elabree/ZeDMD-5.1.8-WIFI-128x32/data/The_Arcade.png

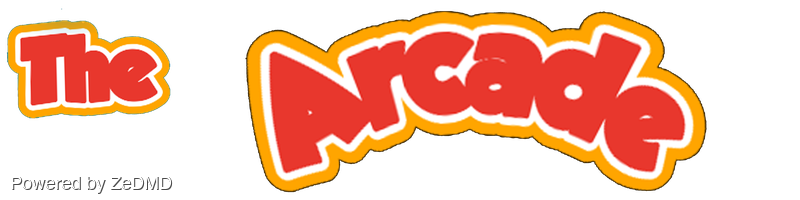
data/The_Arcade.png
