elabree/ZeDMD-5.1.8-WIFI-128x32/docs/images/IMG_5077.jpeg

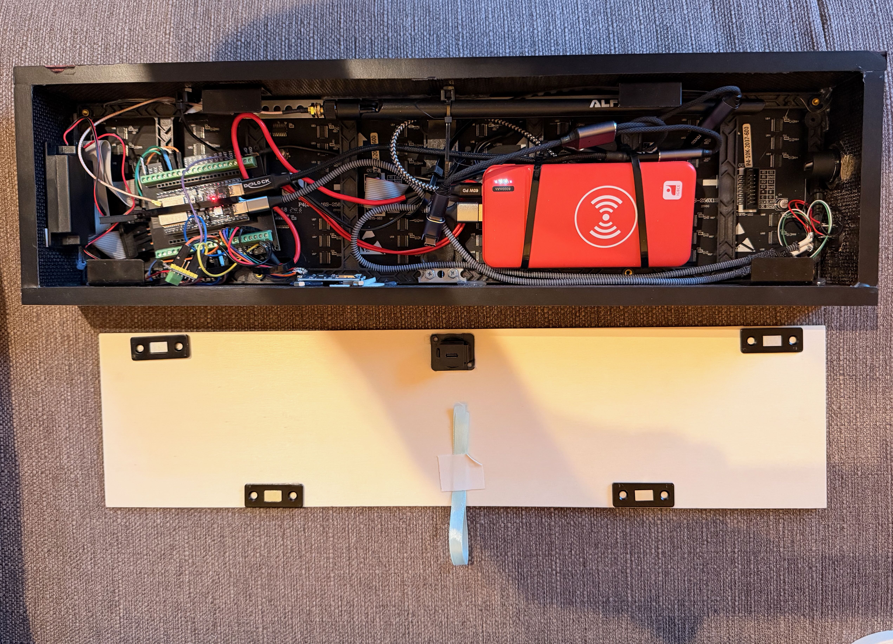
docs/images/IMG_5077.jpeg
