elabree/ZeDMD-5.1.8-WIFI-128x32/KiCad/ZeDMD_WiFi/docs/ZeDMD_WiFi_bottom.png

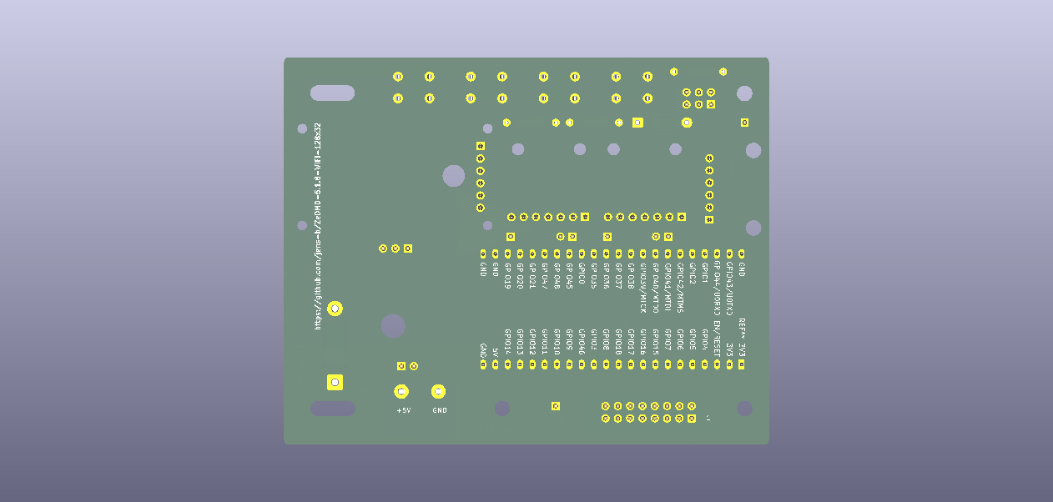
KiCad/ZeDMD_WiFi/docs/ZeDMD_WiFi_bottom.png
