elabree/ZeDMD-5.1.8-WIFI-128x32/src/displayDriver.h

#ifndef DISPLAYDRIVER_H
#define DISPLAYDRIVER_H

#include <stdint.h>

class DisplayDriver {
 public:
  /// @brief Check if display has scaling modes
  /// @return true if scaling modes are available
  virtual bool HasScalingModes() = 0;

  /// @brief Get the names of the scaling modes
  /// @return a static array of scaling mode names
  virtual const char **GetScalingModes() = 0;

  /// @brief Get the number of available scaling modes
  /// @return the count of available scaling modes
  virtual uint8_t GetScalingModeCount() = 0;

  /// @brief Get the current scaling mode
  /// @return the count of available scaling modes
  virtual uint8_t GetCurrentScalingMode() = 0;

  /// @brief Set the scaling mode
  virtual void SetCurrentScalingMode(uint8_t mode) = 0;

  /// @brief Draw a RGB888 pixel
  /// @param x X coordinate
  /// @param y Y coordinate
  /// @param r 8 bit red color
  /// @param g 8 bit green color
  /// @param b 8 bit blue color
  virtual void DrawPixel(uint16_t x, uint16_t y, uint8_t r, uint8_t g,
                         uint8_t b) = 0;

  /// @brief Draw a RGB565 pixel
  /// @param x X coordinate
  /// @param y Y coordinate
  /// @param color 16 bit RGB565 color
  virtual void DrawPixel(uint16_t x, uint16_t y, uint16_t color) = 0;

  /// @brief Clear screen
  virtual void ClearScreen() = 0;

  /// @brief Set brightness of display
  /// @param level 0-15 levels
  virtual void SetBrightness(uint8_t level) = 0;

  /// @brief Fill entire screen with one color
  /// @param r 8 bit red color
  /// @param g 8 bit green color
  /// @param b 8 bit blue color
  virtual void FillScreen(uint8_t r, uint8_t g, uint8_t b) = 0;

  /// @brief Write text to display
  /// @param text string of text
  /// @param x X coordinate
  /// @param y Y coordinate
  /// @param r 8 bit red color
  /// @param g 8 bit green color
  /// @param b 8 bit blue color
  /// @param transparent background transparent
  /// @param inverted colors inverted
  virtual void DisplayText(const char *text, uint16_t x, uint16_t y, uint8_t r,
                           uint8_t g, uint8_t b, bool transparent = false,
                           bool inverted = false) = 0;

  virtual void DisplayTextScaled(const char *text, uint16_t x, uint16_t y,
                                  uint8_t r, uint8_t g, uint8_t b,
                                  uint8_t scale = 1) {
    DisplayText(text, x, y, r, g, b);
  }

#ifdef FONT_TEST_ENABLED
  virtual void RenderFontTestToBuffer(uint8_t * /*buf*/, const char * /*text*/,
                                       const char * /*fontName*/, uint8_t /*lines*/,
                                       uint8_t /*r*/, uint8_t /*g*/, uint8_t /*b*/) {}
  virtual const char* GetFontListJSON() { return "[]"; }
#endif

  virtual void DisplayTextGFX(const char *text, int16_t x, uint8_t r,
                               uint8_t g, uint8_t b) {
    DisplayText(text, (uint16_t)(x < 0 ? 0 : x), 0, r, g, b);
  }

  virtual uint16_t GetTextGFXWidth(const char *text) {
    return (uint16_t)(strlen(text) * 12);
  }

  virtual void EraseVLine(int16_t x) {}
  virtual void RenderTextGFXToBuffer(uint8_t *buf, const char *text, int16_t x,
                                     uint8_t r, uint8_t g, uint8_t b) {}
  virtual void RenderRadioToBuffer(uint8_t *buf, const char *station,
                                   const char *title,
                                   int16_t stationX, int16_t titleX,
                                   uint8_t stR, uint8_t stG, uint8_t stB,
                                   uint8_t r, uint8_t g, uint8_t b) {}
  virtual uint16_t GetRadioTitleWidth(const char *text) {
    return (uint16_t)(strlen(text) * 9);
  }

  /// @brief RGB888 24bit Zone fill
  /// @param idx index
  /// @param pBuffer buffer with pixel data [R,G,B]
  /// @return
  virtual void FillZoneRaw(uint8_t idx, uint8_t *pBuffer) = 0;

  /// @brief RGB565 16 bit Zone Fill
  /// @param idx index
  /// @param pBuffer buffer with pixel data 16 bits
  /// @return
  virtual void FillZoneRaw565(uint8_t idx, uint8_t *pBuffer) = 0;

  virtual void ClearZone(uint8_t idx) = 0;

  /// @brief Fill fullscreen with current renderBuffer
  /// @return
  virtual void FillPanelRaw(uint8_t *pBuffer) = 0;

  virtual ~DisplayDriver() {}  // Virtual destructor
};

#endif  // DISPLAYDRIVER_H
