elabree/ZeDMD-5.1.8-WIFI-128x32/src/displays/LEDMatrix.cpp

#ifdef DISPLAY_LED_MATRIX
#include "LEDMatrix.h"

#include "fonts/tiny4x6.h"
#include <Fonts/FreeSansBold12pt7b.h>
#include <Fonts/FreeSans9pt7b.h>

#ifdef FONT_TEST_ENABLED
#include "fonts/hzeller_tom_thumb.h"
#include "fonts/hzeller_4x6.h"
#include "fonts/hzeller_5x7.h"
#include "fonts/hzeller_5x8.h"
#include "fonts/hzeller_6x9.h"
#include "fonts/hzeller_6x10.h"
#include "fonts/hzeller_6x12.h"
#include "fonts/hzeller_6x13.h"
#include "fonts/hzeller_6x13B.h"
#include "fonts/hzeller_6x13O.h"
#include "fonts/hzeller_7x13.h"
#include "fonts/hzeller_7x13B.h"
#include "fonts/hzeller_7x13O.h"
#include "fonts/hzeller_7x14.h"
#include "fonts/hzeller_7x14B.h"
#include "fonts/hzeller_8x13.h"
#include "fonts/hzeller_8x13B.h"
#include "fonts/hzeller_8x13O.h"
#include "fonts/hzeller_9x15.h"
#include "fonts/hzeller_9x15B.h"
#include "fonts/hzeller_9x18.h"
#include "fonts/hzeller_9x18B.h"
#include "fonts/hzeller_10x20.h"
#include "fonts/hzeller_clR6x12.h"
#include "fonts/hzeller_helvR12.h"
#include "fonts/hzeller_texgyre_27.h"

struct HzFontEntry { const char *name; const GFXfont *font; };
static const HzFontEntry kFonts[] = {
  {"tom-thumb",    &tom_thumb6pt7b},
  {"4x6",          &hz4x66pt7b},
  {"5x7",          &hz5x77pt7b},
  {"5x8",          &hz5x88pt7b},
  {"6x9",          &hz6x99pt7b},
  {"6x10",         &hz6x1010pt7b},
  {"6x12",         &hz6x1212pt7b},
  {"6x13",         &hz6x1313pt7b},
  {"6x13B",        &hz6x13B13pt7b},
  {"6x13O",        &hz6x13O13pt7b},
  {"7x13",         &hz7x1313pt7b},
  {"7x13B",        &hz7x13B13pt7b},
  {"7x13O",        &hz7x13O13pt7b},
  {"7x14",         &hz7x1414pt7b},
  {"7x14B",        &hz7x14B14pt7b},
  {"8x13",         &hz8x1313pt7b},
  {"8x13B",        &hz8x13B13pt7b},
  {"8x13O",        &hz8x13O13pt7b},
  {"9x15",         &hz9x1515pt7b},
  {"9x15B",        &hz9x15B15pt7b},
  {"9x18",         &hz9x1818pt7b},
  {"9x18B",        &hz9x18B18pt7b},
  {"10x20",        &hz10x2020pt7b},
  {"clR6x12",      &clR6x1212pt7b},
  {"helvR12",      &helvR1212pt7b},
  {"texgyre-27",   &texgyre_2727pt7b},
  {"FreeSans9",    &FreeSans9pt7b},
  {"FreeSansBold12", &FreeSansBold12pt7b},
};
static const uint8_t kFontCount = sizeof(kFonts) / sizeof(kFonts[0]);

static const GFXfont* findFont(const char *name) {
  for (uint8_t i = 0; i < kFontCount; i++)
    if (strcmp(kFonts[i].name, name) == 0) return kFonts[i].font;
  return &FreeSans9pt7b;
}

void LedMatrix::RenderFontTestToBuffer(uint8_t *buf, const char *text,
                                        const char *fontName, uint8_t lines,
                                        uint8_t r, uint8_t g, uint8_t b) {
  const GFXfont *f = findFont(fontName);
  memset(buf, 0, (size_t)TOTAL_WIDTH * TOTAL_HEIGHT * 3);
  textCanvas->fillScreen(0);
  textCanvas->setFont(f);
  textCanvas->setTextWrap(false);

  // Cursor y=0: y1 is then a relative offset (negative for ascenders)
  int16_t x1, y1; uint16_t tw, th;
  textCanvas->getTextBounds(text, 0, 0, &x1, &y1, &tw, &th);

  int16_t lineH  = f ? (int16_t)f->yAdvance : (int16_t)th + 1;
  // Total height of the text block (visual pixels)
  int16_t blockH = (int16_t)(lines - 1) * lineH + (int16_t)th;
  // Top edge of the block centered, then derive baseline of the first line
  int16_t topY      = ((int16_t)TOTAL_HEIGHT - blockH) / 2;
  int16_t baseline0 = topY - y1;  // y1 is negative → baseline0 > topY

  // Horizontal centering (same for all lines, same text)
  int16_t cx = ((int16_t)TOTAL_WIDTH - (int16_t)tw) / 2 - x1;
  if (cx < 0) cx = 0;

  uint16_t col = ((uint16_t)(r & 0xF8) << 8) | ((uint16_t)(g & 0xFC) << 3) | (b >> 3);
  textCanvas->setTextColor(col);

  for (uint8_t l = 0; l < lines; l++) {
    int16_t cy = baseline0 + l * lineH;
    if (cy >= (int16_t)TOTAL_HEIGHT) break;
    textCanvas->setCursor(cx, cy);
    textCanvas->print(text);
  }
  textCanvas->setFont(nullptr);

  const uint16_t *pixels = textCanvas->getBuffer();
  const uint32_t n = (uint32_t)TOTAL_WIDTH * TOTAL_HEIGHT;
  for (uint32_t i = 0; i < n; i++) {
    uint16_t c   = pixels[i];
    buf[i * 3]   = (c >> 8) & 0xF8;
    buf[i * 3+1] = (c >> 3) & 0xFC;
    buf[i * 3+2] = (c << 3) & 0xF8;
  }
}

const char* LedMatrix::GetFontListJSON() {
  static char json[768];
  int pos = snprintf(json, sizeof(json), "[");
  for (uint8_t i = 0; i < kFontCount; i++) {
    if (i > 0) pos += snprintf(json + pos, sizeof(json) - pos, ",");
    pos += snprintf(json + pos, sizeof(json) - pos, "\"%s\"", kFonts[i].name);
  }
  snprintf(json + pos, sizeof(json) - pos, "]");
  return json;
}
#endif  // FONT_TEST_ENABLED

// ---------------------------------------------------------------------------
// Emoji system — RGBA icons from LittleFS /icons/ (via main.cpp GetIcon()).
// Icons are loaded into PSRAM at boot (LoadIcons).
// To add: convert PNG (scripts/convert_icons.py), upload .rgba,
// then add a new entry to EMOJI_TABLE.
// ---------------------------------------------------------------------------
static const uint8_t  ICON_W       = 20;   // Source size = target size (2x_larger GIFs)
static const uint8_t  ICON_H       = 20;
static const uint8_t  EMOJI_DRAW_W = 20;
static const uint8_t  EMOJI_DRAW_H = 20;
static const int16_t  EMOJI_Y0     = 5;    // Top-Y: bottom edge at text baseline (y=24)
static const uint8_t  EMOJI_GAP    = 21;   // Advance width (EMOJI_DRAW_W + 1px)

extern const uint8_t* GetIcon(const char* name);       // 20×20 RGBA
extern const uint8_t* GetSmallIcon(const char* name);  // 10×10 RGBA
extern const uint8_t* GetRadioIcon(const char* name);  // 32×32 RGBA

struct EmojiDef {
  const char *utf8;
  const char *iconName;  // filename in /icons/ without .rgba
};

static const EmojiDef EMOJI_TABLE[] = {
  { "\xE2\x9D\xA4",         "heart"        },  // ❤  U+2764
  { "\xE2\xAD\x90",         "star"         },  // ⭐  U+2B50
  { "\xF0\x9F\x8C\x9F",     "star_glow"    },  // 🌟  U+1F31F
  { "\xF0\x9F\x8C\x99",     "moon"         },  // 🌙  U+1F319
  { "\xF0\x9F\x94\xA5",     "fire"         },  // 🔥  U+1F525
  { "\xF0\x9F\x98\x8A",     "smile"        },  // 😊  U+1F60A
  { "\xF0\x9F\x98\x80",     "grin"         },  // 😀  U+1F600
  { "\xF0\x9F\x98\x8E",     "cool"         },  // 😎  U+1F60E
  { "\xF0\x9F\x98\xA1",     "angry"        },  // 😡  U+1F621
  { "\xF0\x9F\x98\xAD",     "cry"          },  // 😭  U+1F62D
  { "\xF0\x9F\x98\xB4",     "sleep"        },  // 😴  U+1F634
  { "\xF0\x9F\x99\x82",     "slight_smile" },  // 🙂  U+1F642
  { "\xF0\x9F\xA4\x94",     "think"        },  // 🤔  U+1F914
  { "\xF0\x9F\xA4\x96",     "robot"        },  // 🤖  U+1F916
  { "\xE2\x9C\x85",         "check"        },  // ✅  U+2705
  { "\xE2\x9D\x8C",         "cross"        },  // ❌  U+274C
  { "\xE2\x9D\x93",         "question"     },  // ❓  U+2753
  { "\xE2\x9D\x97",         "exclaim"      },  // ❗  U+2757
  { "\xF0\x9F\x91\x8D",     "thumbsup"     },  // 👍  U+1F44D
  { "\xF0\x9F\x91\x8E",     "thumbsdown"   },  // 👎  U+1F44E
  { "\xF0\x9F\x8D\x95",     "pizza"        },  // 🍕  U+1F355
  { "\xF0\x9F\x8D\xBA",     "beer"         },  // 🍺  U+1F37A
  { "\xF0\x9F\x8E\x81",     "gift"         },  // 🎁  U+1F381
  { "\xF0\x9F\x8E\x89",     "party"        },  // 🎉  U+1F389
  { "\xF0\x9F\x8E\xAE",     "gamepad"      },  // 🎮  U+1F3AE
  { "\xF0\x9F\x91\xBE",     "alien"        },  // 👾  U+1F47E
  { "\xF0\x9F\x92\xA1",     "bulb"         },  // 💡  U+1F4A1
  { "\xF0\x9F\x92\xB0",     "money"        },  // 💰  U+1F4B0
  { "\xF0\x9F\x93\x9D",     "memo"         },  // 📝  U+1F4DD
  { "\xF0\x9F\x93\xA2",     "speaker"      },  // 📢  U+1F4E2
  { "\xF0\x9F\x93\xB1",     "phone"        },  // 📱  U+1F4F1
  { "\xF0\x9F\x94\x94",     "bell"         },  // 🔔  U+1F514
  { "\xE2\x9A\xA0",         "warning"      },  // ⚠  U+26A0
  { "\xF0\x9F\x8E\xB5",     "note"         },  // 🎵  U+1F3B5
};
static const uint8_t EMOJI_COUNT = sizeof(EMOJI_TABLE) / sizeof(EMOJI_TABLE[0]);

// Returns index into EMOJI_TABLE if *p matches a known emoji, -1 otherwise.
// Advances *p past the matched sequence (incl. optional U+FE0F variation selector).
static int8_t matchEmoji(const char **p) {
  for (uint8_t i = 0; i < EMOJI_COUNT; i++) {
    size_t len = strlen(EMOJI_TABLE[i].utf8);
    if (memcmp(*p, EMOJI_TABLE[i].utf8, len) == 0) {
      *p += len;
      if ((uint8_t)(*p)[0] == 0xEF && (uint8_t)(*p)[1] == 0xB8 && (uint8_t)(*p)[2] == 0x8F)
        *p += 3;
      return (int8_t)i;
    }
  }
  return -1;
}

// Renders a 16×16 RGBA icon (from GetIcon) scaled to EMOJI_DRAW_W×EMOJI_DRAW_H
// into the RGB888 buffer. Transparent pixels (alpha < 32) are skipped.
// shadow=true: RGB is darkened to 1/4 (drop-shadow pass).
static void drawIconRGBAToBuffer(uint8_t *buf, const uint8_t *rgba,
                                  int16_t x, int16_t y0, bool shadow = false) {
  for (uint8_t oy = 0; oy < EMOJI_DRAW_H; oy++) {
    uint8_t sy = (uint8_t)(oy * ICON_H / EMOJI_DRAW_H);
    int16_t py = y0 + oy;
    if (py < 0 || py >= TOTAL_HEIGHT) continue;
    for (uint8_t ox = 0; ox < EMOJI_DRAW_W; ox++) {
      uint8_t sx = (uint8_t)(ox * ICON_W / EMOJI_DRAW_W);
      int16_t px = x + ox;
      if (px < 0 || px >= TOTAL_WIDTH) continue;
      const uint8_t *p = rgba + ((uint16_t)sy * ICON_W + sx) * 4;
      if (p[3] < 32) continue;  // transparent
      uint32_t idx = ((uint32_t)py * TOTAL_WIDTH + px) * 3;
      if (shadow) {
        buf[idx]     = p[0] >> 2;
        buf[idx + 1] = p[1] >> 2;
        buf[idx + 2] = p[2] >> 2;
      } else if (p[3] >= 240) {
        buf[idx]     = p[0];
        buf[idx + 1] = p[1];
        buf[idx + 2] = p[2];
      } else {
        uint8_t a = p[3], ia = 255 - a;
        buf[idx]     = (uint8_t)(((uint16_t)p[0] * a + (uint16_t)buf[idx]     * ia) >> 8);
        buf[idx + 1] = (uint8_t)(((uint16_t)p[1] * a + (uint16_t)buf[idx + 1] * ia) >> 8);
        buf[idx + 2] = (uint8_t)(((uint16_t)p[2] * a + (uint16_t)buf[idx + 2] * ia) >> 8);
      }
    }
  }
}

LedMatrix::LedMatrix() {
  int8_t colorPins1[3] = {R1_PIN, G1_PIN, B1_PIN};
  int8_t colorPins2[3] = {R2_PIN, G2_PIN, B2_PIN};
  const HUB75_I2S_CFG::i2s_pins pins = {colorPins1[rgbOrder[rgbMode * 3]],
                                        colorPins1[rgbOrder[rgbMode * 3 + 1]],
                                        colorPins1[rgbOrder[rgbMode * 3 + 2]],
                                        colorPins2[rgbOrder[rgbMode * 3]],
                                        colorPins2[rgbOrder[rgbMode * 3 + 1]],
                                        colorPins2[rgbOrder[rgbMode * 3 + 2]],
                                        A_PIN,
                                        B_PIN,
                                        C_PIN,
                                        D_PIN,
                                        E_PIN,
                                        LAT_PIN,
                                        OE_PIN,
                                        CLK_PIN};

  HUB75_I2S_CFG mxconfig(PANEL_WIDTH, PANEL_HEIGHT, PANELS_NUMBER, pins);
  // Without setting clkphase to false, HD panels seem to flicker.
  mxconfig.clkphase = (panelClkphase == 1);
  mxconfig.i2sspeed =
      panelI2sspeed == 20
          ? HUB75_I2S_CFG::clk_speed::HZ_20M
          : (panelI2sspeed == 16 ? HUB75_I2S_CFG::clk_speed::HZ_16M
                                 : HUB75_I2S_CFG::clk_speed::HZ_8M);
  mxconfig.latch_blanking = panelLatchBlanking;
  mxconfig.min_refresh_rate = panelMinRefreshRate;
  mxconfig.driver = (HUB75_I2S_CFG::shift_driver)panelDriver;
  mxconfig.line_decoder = (HUB75_I2S_CFG::line_driver)panelLineDecoder;

  dma_display = new MatrixPanel_I2S_DMA(mxconfig);
  dma_display->begin();

  // Pre-allocated canvas for flicker-free GFX text rendering.
  // Renders into SRAM pixel-by-pixel without touching the live DMA buffer.
  textCanvas = new GFXcanvas16(TOTAL_WIDTH, TOTAL_HEIGHT);
}

bool LedMatrix::HasScalingModes() {
  return false;  // This display does not support subpixel scaling
}

const char **LedMatrix::GetScalingModes() { return nullptr; }

uint8_t LedMatrix::GetScalingModeCount() { return 0; }

uint8_t LedMatrix::GetCurrentScalingMode() { return 0; }

void LedMatrix::SetCurrentScalingMode(uint8_t mode) {}

void LedMatrix::DrawPixel(uint16_t x, uint16_t y, uint8_t r, uint8_t g,
                          uint8_t b) {
  dma_display->drawPixelRGB888(x, y + yOffset, r, g, b);
}

void LedMatrix::DrawPixel(uint16_t x, uint16_t y, uint16_t color) {
  dma_display->drawPixel(x, y + yOffset, color);
}

void LedMatrix::ClearScreen() { dma_display->clearScreen(); }

void LedMatrix::SetBrightness(uint8_t level) {
  dma_display->setBrightness8(lumval[level]);
}

void LedMatrix::FillScreen(uint8_t r, uint8_t g, uint8_t b) {
  dma_display->fillScreenRGB888(r, g, b);
}

void LedMatrix::DisplayText(const char *text, uint16_t x, uint16_t y, uint8_t r,
                            uint8_t g, uint8_t b, bool transparent,
                            bool inverted) {
  for (uint8_t ti = 0; ti < strlen(text); ti++) {
    for (uint8_t tj = 0; tj <= 5; tj++) {
      uint8_t fourPixels = getFontLine(text[ti], tj);
      for (uint8_t pixel = 0; pixel < 4; pixel++) {
        bool p = (fourPixels >> (3 - pixel)) & 0x1;
        if (inverted) {
          p = !p;
        }
        if (transparent && !p) {
          continue;
        }
        DrawPixel(x + pixel + (ti * 4), y + tj, r * p, g * p, b * p);
      }
    }
  }
}

void LedMatrix::DisplayTextScaled(const char *text, uint16_t x, uint16_t y,
                                   uint8_t r, uint8_t g, uint8_t b, uint8_t scale) {
  if (scale <= 1) { DisplayText(text, x, y, r, g, b); return; }
  for (uint8_t ti = 0; ti < strlen(text); ti++) {
    for (uint8_t tj = 0; tj < 6; tj++) {
      uint8_t fourPixels = getFontLine(text[ti], tj);
      for (uint8_t pixel = 0; pixel < 4; pixel++) {
        if (!((fourPixels >> (3 - pixel)) & 0x1)) continue;
        for (uint8_t sy = 0; sy < scale; sy++)
          for (uint8_t sx = 0; sx < scale; sx++)
            DrawPixel(x + (pixel + ti * 4) * scale + sx,
                      y + tj * scale + sy, r, g, b);
      }
    }
  }
}

void IRAM_ATTR LedMatrix::FillZoneRaw(uint8_t idx, uint8_t *pBuffer) {
  const uint8_t zoneYOffset = (idx / ZONES_PER_ROW) * ZONE_HEIGHT;
  const uint8_t zoneXOffset = (idx % ZONES_PER_ROW) * ZONE_WIDTH;

  for (uint8_t y = 0; y < ZONE_HEIGHT; y++) {
    for (uint8_t x = 0; x < ZONE_WIDTH; x++) {
      uint16_t pos = (y * ZONE_WIDTH + x) * 3;

      DrawPixel(x + zoneXOffset, y + zoneYOffset, pBuffer[pos],
                pBuffer[pos + 1], pBuffer[pos + 2]);
    }
  }
}

void IRAM_ATTR LedMatrix::FillZoneRaw565(uint8_t idx, uint8_t *pBuffer) {
  const uint8_t zoneYOffset = (idx / ZONES_PER_ROW) * ZONE_HEIGHT;
  const uint8_t zoneXOffset = (idx % ZONES_PER_ROW) * ZONE_WIDTH;

  for (uint8_t y = 0; y < ZONE_HEIGHT; y++) {
    for (uint8_t x = 0; x < ZONE_WIDTH; x++) {
      uint16_t pos = (y * ZONE_WIDTH + x) * 2;
      DrawPixel(x + zoneXOffset, y + zoneYOffset,
                (((uint16_t)pBuffer[pos + 1]) << 8) + pBuffer[pos]);
    }
  }
}

void IRAM_ATTR LedMatrix::ClearZone(uint8_t idx) {
  const uint8_t zoneYOffset = (idx / ZONES_PER_ROW) * ZONE_HEIGHT;
  const uint8_t zoneXOffset = (idx % ZONES_PER_ROW) * ZONE_WIDTH;

  for (uint8_t y = 0; y < ZONE_HEIGHT; y++) {
    for (uint8_t x = 0; x < ZONE_WIDTH; x++) {
      DrawPixel(x + zoneXOffset, y + zoneYOffset, 0, 0, 0);
    }
  }
}

void IRAM_ATTR LedMatrix::FillPanelRaw(uint8_t *pBuffer) {
  uint16_t pos;

  for (uint16_t y = 0; y < TOTAL_HEIGHT; y++) {
    for (uint16_t x = 0; x < TOTAL_WIDTH; x++) {
      pos = (y * TOTAL_WIDTH + x) * 3;

      DrawPixel(x, y, pBuffer[pos], pBuffer[pos + 1], pBuffer[pos + 2]);
    }
  }
}

// Renders text with FreeSansBold12pt7b (~17px tall). x may be negative (clips correctly).
// Baseline y=24 leaves headroom for ascenders and descenders within 32px display height.
void LedMatrix::DisplayTextGFX(const char *text, int16_t x, uint8_t r,
                                uint8_t g, uint8_t b) {
  dma_display->setFont(&FreeSansBold12pt7b);
  // Black background fills each glyph cell — avoids ClearScreen() between frames
  dma_display->setTextColor(dma_display->color565(r, g, b), 0x0000);
  dma_display->setTextWrap(false);
  dma_display->setCursor(x, 24);
  dma_display->print(text);
  dma_display->setFont(nullptr);
}

void LedMatrix::EraseVLine(int16_t x) {
  if (x >= 0 && x < dma_display->width())
    dma_display->drawFastVLine(x, 0, dma_display->height(), 0);
}

// Converts UTF-8 and Latin-1 umlauts to ASCII substitutions (ä→ae, ö→oe, …).
// Unknown high bytes are skipped. All other bytes are copied 1:1.
static void latinToAscii(const char *src, char *dst, size_t dstLen) {
  size_t d = 0;
  for (size_t i = 0; src[i] && d + 4 < dstLen; i++) {
    uint8_t c = (uint8_t)src[i];
    if      (c < 0x80) { dst[d++] = (char)c; }      // ASCII 1:1
    else if (c == 0xC3 && src[i + 1]) {              // UTF-8 C3xx: German umlauts
      uint8_t n = (uint8_t)src[++i];
      const char *s = n==0x84?"Ae": n==0x96?"Oe": n==0x9C?"Ue":
                      n==0xA4?"ae": n==0xB6?"oe": n==0xBC?"ue":
                      n==0x9F?"ss": nullptr;
      if (s) { while (*s && d < dstLen - 1) dst[d++] = *s++; }
      else   { dst[d++] = 0xC3; dst[d++] = (char)n; } // unknown C3 sequence: pass through unchanged
    }
    else if (c == 0xC4) { dst[d++] = 'A'; dst[d++] = 'e'; } // Latin-1 Ä
    else if (c == 0xD6) { dst[d++] = 'O'; dst[d++] = 'e'; } // Latin-1 Ö
    else if (c == 0xDC) { dst[d++] = 'U'; dst[d++] = 'e'; } // Latin-1 Ü
    else if (c == 0xE4) { dst[d++] = 'a'; dst[d++] = 'e'; } // Latin-1 ä
    else if (c == 0xF6) { dst[d++] = 'o'; dst[d++] = 'e'; } // Latin-1 ö
    else if (c == 0xFC) { dst[d++] = 'u'; dst[d++] = 'e'; } // Latin-1 ü
    else if (c == 0xDF) { dst[d++] = 's'; dst[d++] = 's'; } // Latin-1 ß
    else if (c >= 0xE0) {
      // 3- or 4-byte UTF-8 sequence (Emoji etc.): pass all bytes through unchanged
      uint8_t seqLen = (c >= 0xF0) ? 4 : 3;
      if (d + seqLen < dstLen) {
        dst[d++] = (char)c;
        for (uint8_t j = 1; j < seqLen && src[i + j]; j++) dst[d++] = src[i + j];
        i += seqLen - 1;
      }
    }
    // 0x80-0xDF: orphaned continuation bytes or unknown 2-byte leads → skip
  }
  dst[d] = '\0';
}

// Returns advance width of radio title text rendered with FreeSans9pt7b.
uint16_t LedMatrix::GetRadioTitleWidth(const char *text) {
  char buf[256];
  latinToAscii(text, buf, sizeof(buf));
  textCanvas->setFont(&FreeSans9pt7b);
  int16_t x1, y1; uint16_t w, h;
  textCanvas->getTextBounds(buf, 0, 0, &x1, &y1, &w, &h);
  textCanvas->setFont(nullptr);
  return w;
}

// Returns pixel width of text rendered with FreeSansBold12pt7b + inline emojis.
uint16_t LedMatrix::GetTextGFXWidth(const char *text) {
  // Build a plain-text copy with emojis replaced by spaces for font measurement,
  // then add 11px per emoji (10px bitmap + 1px gap).
  char converted[256];
  latinToAscii(text, converted, sizeof(converted));
  char plain[256];
  uint8_t emojiCount = 0;
  const char *src = converted;
  char *dst = plain;
  while (*src && dst < plain + sizeof(plain) - 1) {
    int8_t idx = matchEmoji(&src);
    if (idx >= 0) {
      emojiCount++;
    } else {
      *dst++ = *src++;
    }
  }
  *dst = '\0';

  uint16_t textW = 0;
  if (*plain) {
    textCanvas->setFont(&FreeSansBold12pt7b);
    textCanvas->setCursor(0, 24);
    textCanvas->print(plain);
    textW = (uint16_t)textCanvas->getCursorX();
    textCanvas->setFont(nullptr);
  }
  return textW + (uint16_t)emojiCount * EMOJI_GAP;
}

// Renders text + inline emojis at position x into an RGB888 renderBuffer.
// Text is rendered in segments between emojis so each part lands at the correct
// x position — no overlap between text and emoji bitmaps.
void LedMatrix::RenderTextGFXToBuffer(uint8_t *buf, const char *text, int16_t x,
                                       uint8_t r, uint8_t g, uint8_t b) {
  char converted[256];
  latinToAscii(text, converted, sizeof(converted));

  textCanvas->fillScreen(0);
  uint16_t color565 = ((uint16_t)(r & 0xF8) << 8) | ((uint16_t)(g & 0xFC) << 3) | (b >> 3);
  textCanvas->setFont(&FreeSansBold12pt7b);
  textCanvas->setTextColor(color565);
  textCanvas->setTextWrap(false);

  struct EmojiPlacement { int16_t x; uint8_t idx; };
  EmojiPlacement placements[16];
  uint8_t numPlacements = 0;

  const char *src = converted;
  int16_t curX = x;
  char seg[128];
  char *dst = seg;

  while (*src) {
    int8_t idx = matchEmoji(&src);
    if (idx >= 0) {
      // Render accumulated text segment at curX, then advance curX by its width
      if (dst > seg) {
        *dst = '\0';
        textCanvas->setCursor(curX, 24);
        textCanvas->print(seg);
        curX = textCanvas->getCursorX();
        dst = seg;
      }
      if (numPlacements < 16)
        placements[numPlacements++] = { curX, (uint8_t)idx };
      curX += EMOJI_GAP;
    } else if (dst < seg + sizeof(seg) - 1) {
      *dst++ = *src++;
    } else {
      src++;  // buffer full — skip character
    }
  }
  // Flush remaining text segment
  if (dst > seg) {
    *dst = '\0';
    textCanvas->setCursor(curX, 24);
    textCanvas->print(seg);
  }
  textCanvas->setFont(nullptr);

  // Copy canvas → RGB888 buffer
  const uint16_t *pixels = textCanvas->getBuffer();
  const uint32_t n = TOTAL_WIDTH * TOTAL_HEIGHT;
  for (uint32_t i = 0; i < n; i++) {
    uint16_t c      = pixels[i];
    buf[i * 3]     = (c >> 8) & 0xF8;
    buf[i * 3 + 1] = (c >> 3) & 0xFC;
    buf[i * 3 + 2] = (c << 3) & 0xF8;
  }

  // Composite RGBA icons into buf — shadow (+1/+1 darkened), then icon on top
  for (uint8_t i = 0; i < numPlacements; i++) {
    const uint8_t *rgba = GetIcon(EMOJI_TABLE[placements[i].idx].iconName);
    if (!rgba) continue;  // icon not loaded — skip
    drawIconRGBAToBuffer(buf, rgba, placements[i].x + 1, EMOJI_Y0 + 1, true);
    drawIconRGBAToBuffer(buf, rgba, placements[i].x,     EMOJI_Y0,      false);
  }
}

// Two-row radio display:
//   Icon: 32×32 (station logo /icons_radio/ or fallback note), x=0..31
//   Top:  FreeSans9pt7b, yellow, baseline y=13, x=32..127, centered
//   Sep:  y=15, x=32..127
//   Bot:  FreeSans9pt7b, scrolling from titleX, baseline y=29, x=32..127
static const uint8_t RADIO_ICON_W = 32;

// 32×32 RGBA fallback icon (eighth note ♫), steel blue 3D, navy-blue outline
static const uint8_t RADIO_FALLBACK_ICON[4096] PROGMEM = {
  0x00, 0x00, 0x00, 0x00, 0x00, 0x00, 0x00, 0x00, 0x00, 0x00, 0x00, 0x00, 0x00, 0x00, 0x00, 0x00,
  0x00, 0x00, 0x00, 0x00, 0x00, 0x00, 0x00, 0x00, 0x00, 0x00, 0x00, 0x00, 0x00, 0x00, 0x00, 0x00,
  0x00, 0x00, 0x00, 0x00, 0x00, 0x00, 0x00, 0x00, 0x00, 0x00, 0x00, 0x00, 0x00, 0x00, 0x00, 0x00,
  0x00, 0x00, 0x00, 0x00, 0x00, 0x00, 0x00, 0x00, 0x00, 0x00, 0x00, 0x00, 0x00, 0x00, 0x00, 0x00,
  0x00, 0x00, 0x00, 0x00, 0x00, 0x00, 0x00, 0x00, 0x00, 0x00, 0x00, 0x00, 0x00, 0x00, 0x00, 0x00,
  0x00, 0x00, 0x00, 0x00, 0x00, 0x00, 0x00, 0x00, 0x00, 0x00, 0x00, 0x00, 0x00, 0x00, 0x00, 0x00,
  0x00, 0x00, 0x00, 0x00, 0x00, 0x00, 0x00, 0x00, 0x00, 0x00, 0x00, 0x00, 0x00, 0x00, 0x00, 0x00,
  0x00, 0x00, 0x00, 0x00, 0x00, 0x00, 0x00, 0x00, 0x00, 0x00, 0x00, 0x00, 0x00, 0x00, 0x00, 0x00,
  0x00, 0x00, 0x00, 0x00, 0x00, 0x00, 0x00, 0x00, 0x00, 0x00, 0x00, 0x00, 0x00, 0x00, 0x00, 0x00,
  0x00, 0x00, 0x00, 0x00, 0x00, 0x00, 0x00, 0x00, 0x00, 0x00, 0x00, 0x00, 0x00, 0x00, 0x00, 0x00,
  0x00, 0x00, 0x00, 0x00, 0x00, 0x00, 0x00, 0x00, 0x00, 0x00, 0x00, 0x00, 0x00, 0x00, 0x00, 0x00,
  0x00, 0x00, 0x00, 0x00, 0x00, 0x00, 0x00, 0x00, 0x00, 0x00, 0x00, 0x00, 0x00, 0x00, 0x00, 0x00,
  0x00, 0x00, 0x00, 0x00, 0x00, 0x00, 0x00, 0x00, 0x00, 0x00, 0x00, 0x00, 0x00, 0x00, 0x00, 0x00,
  0x00, 0x00, 0x00, 0x00, 0x00, 0x00, 0x00, 0x00, 0x16, 0x22, 0x34, 0xff, 0x16, 0x22, 0x34, 0xff,
  0x16, 0x22, 0x34, 0xff, 0x16, 0x22, 0x34, 0xff, 0x16, 0x22, 0x34, 0xff, 0xa8, 0xc8, 0xde, 0xff,
  0x16, 0x22, 0x34, 0xff, 0x00, 0x00, 0x00, 0x00, 0x00, 0x00, 0x00, 0x00, 0x00, 0x00, 0x00, 0x00,
  0x00, 0x00, 0x00, 0x00, 0x00, 0x00, 0x00, 0x00, 0x00, 0x00, 0x00, 0x00, 0x00, 0x00, 0x00, 0x00,
  0x00, 0x00, 0x00, 0x00, 0x00, 0x00, 0x00, 0x00, 0x00, 0x00, 0x00, 0x00, 0x00, 0x00, 0x00, 0x00,
  0x00, 0x00, 0x00, 0x00, 0x00, 0x00, 0x00, 0x00, 0x00, 0x00, 0x00, 0x00, 0x00, 0x00, 0x00, 0x00,
  0x00, 0x00, 0x00, 0x00, 0x00, 0x00, 0x00, 0x00, 0x00, 0x00, 0x00, 0x00, 0x00, 0x00, 0x00, 0x00,
  0x16, 0x22, 0x34, 0xff, 0x16, 0x22, 0x34, 0xff, 0x16, 0x22, 0x34, 0xff, 0x16, 0x22, 0x34, 0xff,
  0x16, 0x22, 0x34, 0xff, 0x16, 0x22, 0x34, 0xff, 0xa8, 0xc8, 0xde, 0xff, 0xa8, 0xc8, 0xde, 0xff,
  0xa8, 0xc8, 0xde, 0xff, 0xa8, 0xc8, 0xde, 0xff, 0xa8, 0xc8, 0xde, 0xff, 0x3a, 0x54, 0x70, 0xff,
  0x16, 0x22, 0x34, 0xff, 0x00, 0x00, 0x00, 0x00, 0x00, 0x00, 0x00, 0x00, 0x00, 0x00, 0x00, 0x00,
  0x00, 0x00, 0x00, 0x00, 0x00, 0x00, 0x00, 0x00, 0x00, 0x00, 0x00, 0x00, 0x00, 0x00, 0x00, 0x00,
  0x00, 0x00, 0x00, 0x00, 0x00, 0x00, 0x00, 0x00, 0x00, 0x00, 0x00, 0x00, 0x00, 0x00, 0x00, 0x00,
  0x00, 0x00, 0x00, 0x00, 0x00, 0x00, 0x00, 0x00, 0x16, 0x22, 0x34, 0xff, 0x16, 0x22, 0x34, 0xff,
  0x16, 0x22, 0x34, 0xff, 0x16, 0x22, 0x34, 0xff, 0x16, 0x22, 0x34, 0xff, 0x16, 0x22, 0x34, 0xff,
  0xa8, 0xc8, 0xde, 0xff, 0xa8, 0xc8, 0xde, 0xff, 0xa8, 0xc8, 0xde, 0xff, 0xa8, 0xc8, 0xde, 0xff,
  0xa8, 0xc8, 0xde, 0xff, 0xa8, 0xc8, 0xde, 0xff, 0xa8, 0xc8, 0xde, 0xff, 0x62, 0x8a, 0xa8, 0xff,
  0x62, 0x8a, 0xa8, 0xff, 0x62, 0x8a, 0xa8, 0xff, 0xa8, 0xc8, 0xde, 0xff, 0x3a, 0x54, 0x70, 0xff,
  0x16, 0x22, 0x34, 0xff, 0x00, 0x00, 0x00, 0x00, 0x00, 0x00, 0x00, 0x00, 0x00, 0x00, 0x00, 0x00,
  0x00, 0x00, 0x00, 0x00, 0x00, 0x00, 0x00, 0x00, 0x00, 0x00, 0x00, 0x00, 0x00, 0x00, 0x00, 0x00,
  0x00, 0x00, 0x00, 0x00, 0x00, 0x00, 0x00, 0x00, 0x00, 0x00, 0x00, 0x00, 0x00, 0x00, 0x00, 0x00,
  0x00, 0x00, 0x00, 0x00, 0x00, 0x00, 0x00, 0x00, 0x16, 0x22, 0x34, 0xff, 0xa8, 0xc8, 0xde, 0xff,
  0x3a, 0x54, 0x70, 0xff, 0xa8, 0xc8, 0xde, 0xff, 0xa8, 0xc8, 0xde, 0xff, 0xa8, 0xc8, 0xde, 0xff,
  0xa8, 0xc8, 0xde, 0xff, 0x62, 0x8a, 0xa8, 0xff, 0x62, 0x8a, 0xa8, 0xff, 0x62, 0x8a, 0xa8, 0xff,
  0x62, 0x8a, 0xa8, 0xff, 0x62, 0x8a, 0xa8, 0xff, 0x62, 0x8a, 0xa8, 0xff, 0x62, 0x8a, 0xa8, 0xff,
  0x62, 0x8a, 0xa8, 0xff, 0x62, 0x8a, 0xa8, 0xff, 0xa8, 0xc8, 0xde, 0xff, 0x3a, 0x54, 0x70, 0xff,
  0x16, 0x22, 0x34, 0xff, 0x00, 0x00, 0x00, 0x00, 0x00, 0x00, 0x00, 0x00, 0x00, 0x00, 0x00, 0x00,
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
};


static void stationToSlug(const char *station, char *out, size_t outLen) {
  size_t j = 0;
  for (size_t i = 0; station[i] && j + 1 < outLen; i++) {
    char c = station[i];
    if (c >= 'A' && c <= 'Z') c += 32;
    if ((c >= 'a' && c <= 'z') || (c >= '0' && c <= '9'))
      out[j++] = c;
    else if (j > 0 && out[j - 1] != '_')
      out[j++] = '_';
  }
  while (j > 0 && out[j - 1] == '_') j--;
  out[j] = '\0';
}

void LedMatrix::RenderRadioToBuffer(uint8_t *buf, const char *station,
                                    const char *title,
                                    int16_t stationX, int16_t titleX,
                                    uint8_t stR, uint8_t stG, uint8_t stB,
                                    uint8_t r, uint8_t g, uint8_t b) {
  char stationA[128];
  char titleA[256];
  latinToAscii(station, stationA, sizeof(stationA));
  latinToAscii(title,   titleA,   sizeof(titleA));
  station = stationA;
  title   = titleA;

  // --- Canvas: all at once (station name + separator + title) ---
  textCanvas->fillScreen(0);
  textCanvas->setFont(&FreeSans9pt7b);
  textCanvas->setTextWrap(false);

  // Station name: clock color, position from caller (centered or scrolling)
  {
    uint16_t stColor = ((uint16_t)(stR & 0xF8) << 8) | ((uint16_t)(stG & 0xFC) << 3) | (stB >> 3);
    textCanvas->setTextColor(stColor);
    textCanvas->setCursor(stationX, 13);
    textCanvas->print(station);
  }

  // Separator
  uint16_t grey = ((uint16_t)(60 & 0xF8) << 8) | ((uint16_t)(60 & 0xFC) << 3) | (60 >> 3);
  textCanvas->drawFastHLine(RADIO_ICON_W, 15, TOTAL_WIDTH - RADIO_ICON_W, grey);

  // Title: scrolling, baseline y=29
  {
    uint16_t col = ((uint16_t)(r & 0xF8) << 8) | ((uint16_t)(g & 0xFC) << 3) | (b >> 3);
    textCanvas->setTextColor(col);
    textCanvas->setCursor(titleX, 29);
    textCanvas->print(title);
  }

  textCanvas->setFont(nullptr);

  // Canvas → RGB888 Buffer
  const uint16_t *pixels = textCanvas->getBuffer();
  const uint32_t n = TOTAL_WIDTH * TOTAL_HEIGHT;
  for (uint32_t i = 0; i < n; i++) {
    uint16_t c      = pixels[i];
    buf[i * 3]     = (c >> 8) & 0xF8;
    buf[i * 3 + 1] = (c >> 3) & 0xFC;
    buf[i * 3 + 2] = (c << 3) & 0xF8;
  }

  // Icon area to black
  for (uint8_t cy = 0; cy < TOTAL_HEIGHT; cy++)
    for (uint8_t cx = 0; cx < RADIO_ICON_W; cx++) {
      uint32_t pos = ((uint32_t)cy * TOTAL_WIDTH + cx) * 3;
      buf[pos] = buf[pos + 1] = buf[pos + 2] = 0;
    }

  // --- Icon 32×32: LittleFS logo or fallback note ---
  char slug[32];
  stationToSlug(station, slug, sizeof(slug));
  const uint8_t *icon = GetRadioIcon(slug);  // incl. fuzzy match in GetRadioIcon()
  if (!icon) icon = RADIO_FALLBACK_ICON;

  for (uint8_t iy = 0; iy < 32; iy++) {
    for (uint8_t ix = 0; ix < 32; ix++) {
      const uint8_t *px = icon + ((uint32_t)iy * 32 + ix) * 4;
      uint8_t a = px[3];
      if (a == 0) continue;
      uint32_t pos = ((uint32_t)iy * TOTAL_WIDTH + ix) * 3;
      buf[pos]     = (uint8_t)((uint32_t)px[0] * a / 255);
      buf[pos + 1] = (uint8_t)((uint32_t)px[1] * a / 255);
      buf[pos + 2] = (uint8_t)((uint32_t)px[2] * a / 255);
    }
  }
}

LedMatrix::~LedMatrix() {
  delete textCanvas;
  delete dma_display;
}
#endif
