elabree/ZeDMD-5.1.8-WIFI-128x32/src/version.h

#ifndef VERSION_H
#define VERSION_H

// Version constants
#define ZEDMD_VERSION_MAJOR 5
#define ZEDMD_VERSION_MINOR 1
#define ZEDMD_VERSION_PATCH 8
#define ZEDMD_VERSION_SUFFIX "-jb"

#endif  // VERSION_H
